Gfermoto/UAV-radar/docs/assets/diy/hero-mic.jpg

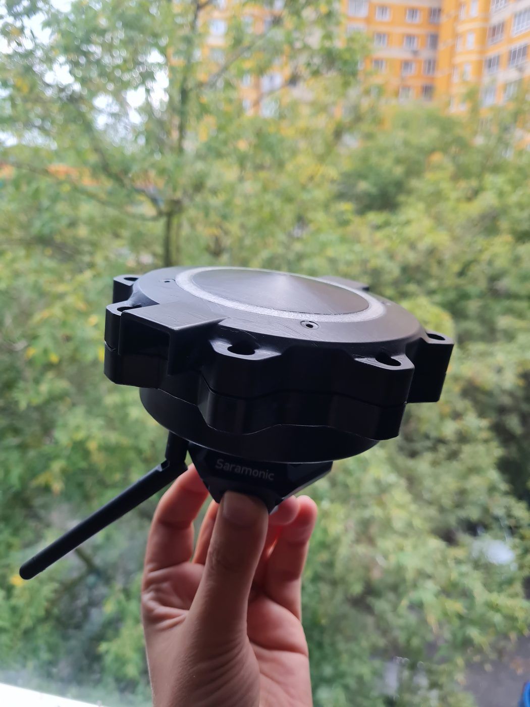
docs/assets/diy/hero-mic.jpg
