Gfermoto/UAV-radar/docs/assets/og-default.png

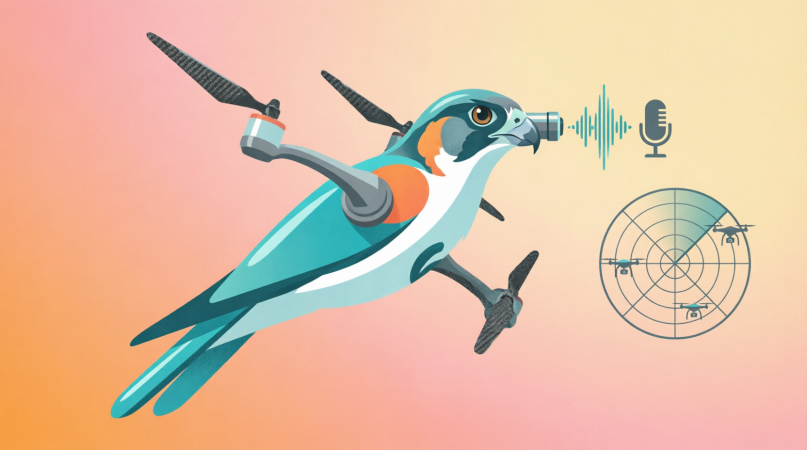
docs/assets/og-default.png
