Gfermoto/UAV-radar/docs/assets/og-social.png

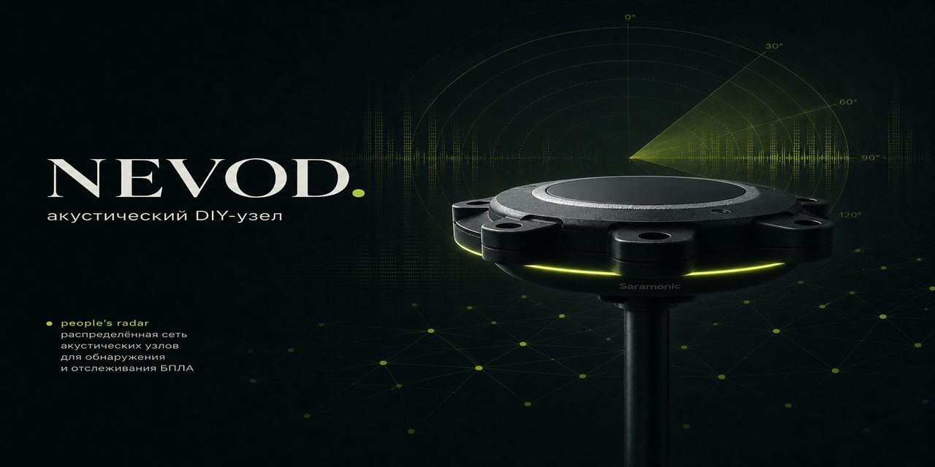
docs/assets/og-social.png
