Gfermoto/UAV-radar/src/mel_lut.h

/**
 * @file    mel_lut.h
 * @brief   Compile-time MEL LUT — Hann window + sparse filterbank.
 *
 * Сгенерировано: tools/generate_mel_lut.py
 * НЕ РЕДАКТИРОВАТЬ ВРУЧНУЮ — перегенерировать скриптом.
 *
 * Параметры:
 *   Fs = 16000 Гц, FFT = 512, бинов = 257
 *   MEL = 64 полос, 125–7500 Гц, HTK-формула
 *   Окно Ханна: 400 точек + 112 zero-pad
 *
 * Память (flash):
 *   MEL_HANN_WINDOW:   2.0 KB
 *   Sparse filterbank: ~1.93 KB (was dense 64.2 KB)
 *
 * Sparse filterbank: MEL_FB_START[b], MEL_FB_LEN[b], MEL_FB_OFFSET[b], MEL_FB_WEIGHTS[]
 * — только ненулевые веса (~1.93 KB flash vs dense 64.2 KB).
 *
 * @see MelSpectrogram.h, tools/generate_mel_lut.py, docs/ARCHITECTURE.md
 */

#ifndef MEL_LUT_H
#define MEL_LUT_H

#include <Arduino.h>
#include <cstdint>

// ---- Размерности (из Config.h) ----

#define MEL_LUT_NUM_BANDS  64
#define MEL_LUT_FFT_SIZE   512
#define MEL_LUT_NUM_BINS   257

// ---- Окно Ханна (512 float) ----

static const float MEL_HANN_WINDOW[] = {
    0.00000000f, 0.00006199f, 0.00024796f, 0.00055785f, 0.00099159f, 0.00154906f, 0.00223015f, 0.00303466f,
    0.00396241f, 0.00501316f, 0.00618666f, 0.00748261f, 0.00890069f, 0.01044055f, 0.01210181f, 0.01388405f,
    0.01578684f, 0.01780970f, 0.01995213f, 0.02221360f, 0.02459354f, 0.02709138f, 0.02970648f, 0.03243821f,
    0.03528587f, 0.03824878f, 0.04132618f, 0.04451733f, 0.04782142f, 0.05123764f, 0.05476514f, 0.05840305f,
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
    0.28571429f, 0.14285714f, 0.14285714f, 0.28571429f, 0.42857143f, 0.57142857f, 0.71428571f, 0.85714286f,
    1.00000000f, 0.87500000f, 0.75000000f, 0.62500000f, 0.50000000f, 0.37500000f, 0.25000000f, 0.12500000f,
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
};

#endif // MEL_LUT_H
